MaruTama/ArduinoNameCard/res/img/3Dviewer.png

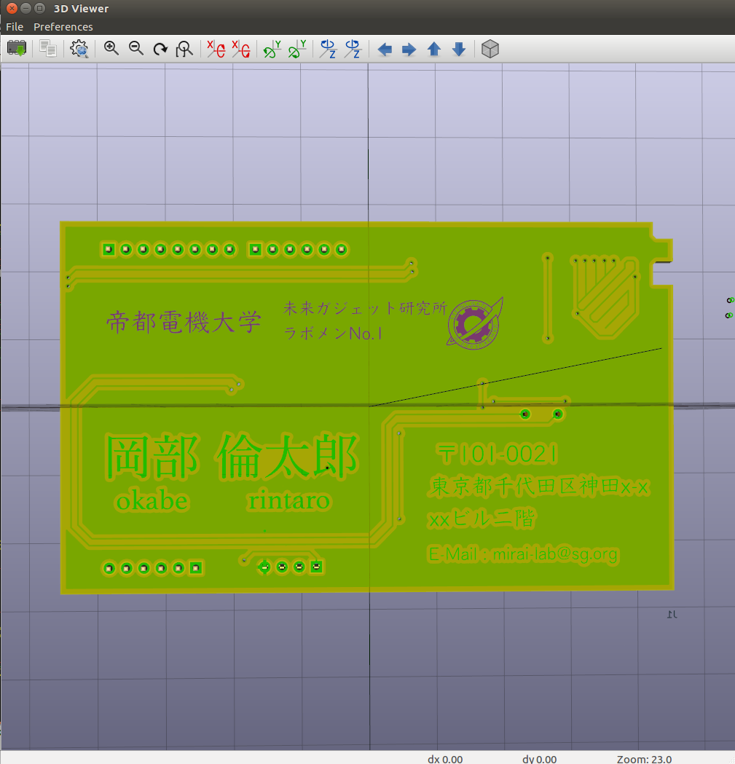
res/img/3Dviewer.png
