MaruTama/ArduinoNameCard/res/img/affiliation.png

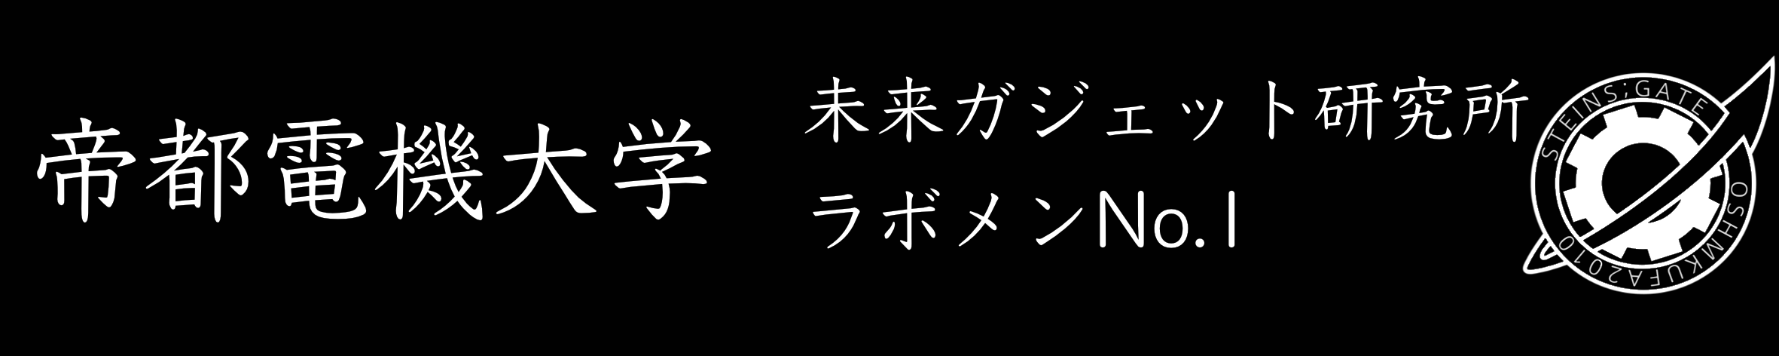
res/img/affiliation.png
