MaruTama/ArduinoNameCard/res/img/apply_footprint.png

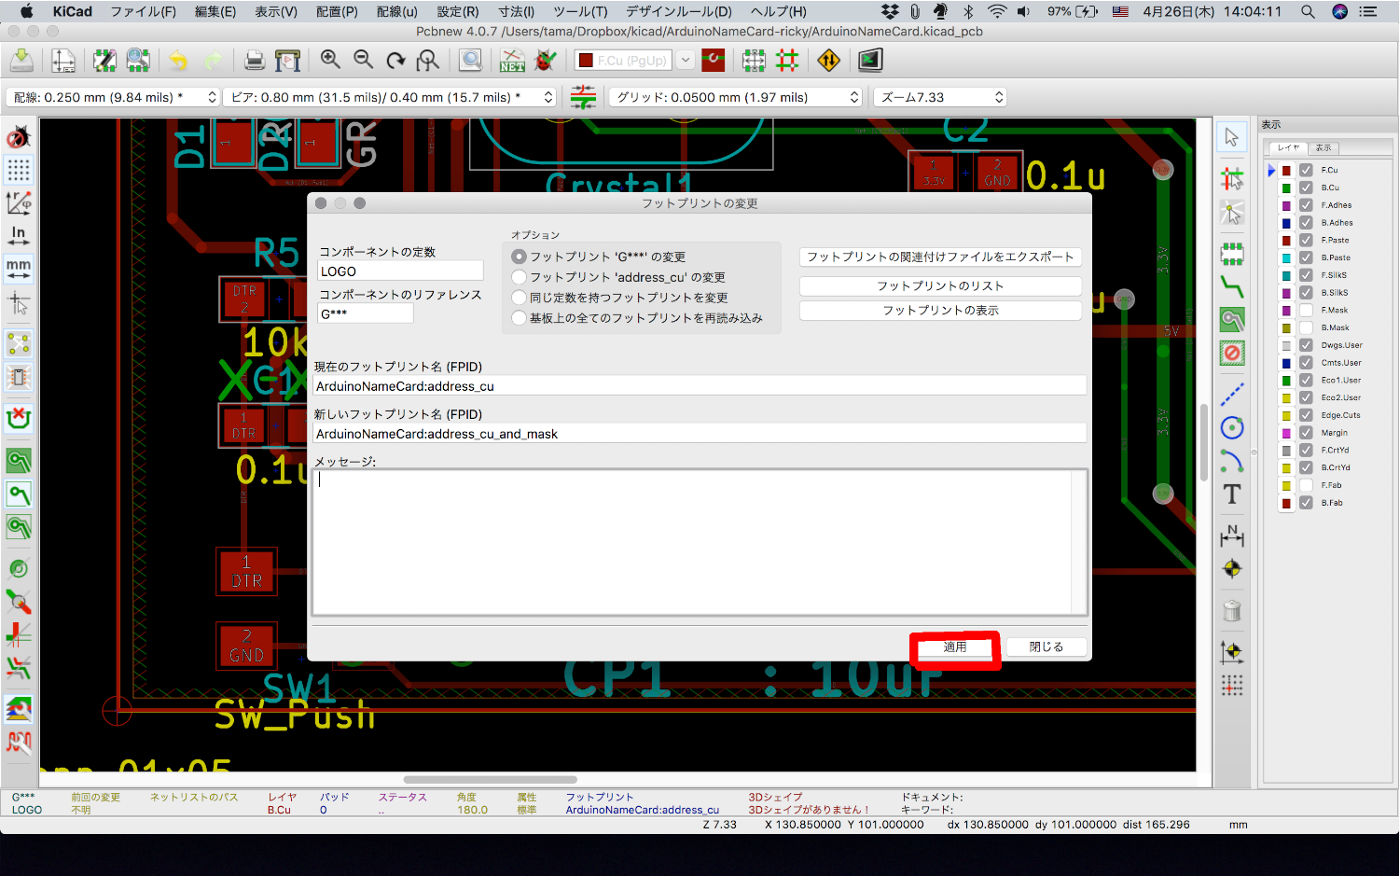
res/img/apply_footprint.png
