MaruTama/ArduinoNameCard/res/img/back_of_card.png

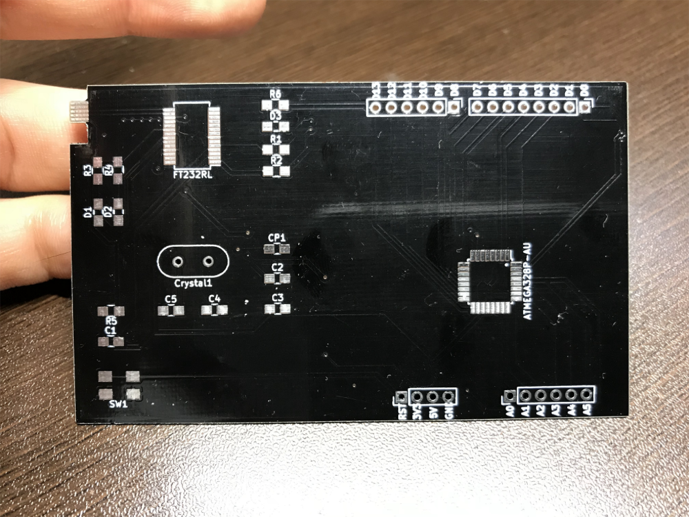
res/img/back_of_card.png
