MaruTama/ArduinoNameCard/res/img/bottom_black.png

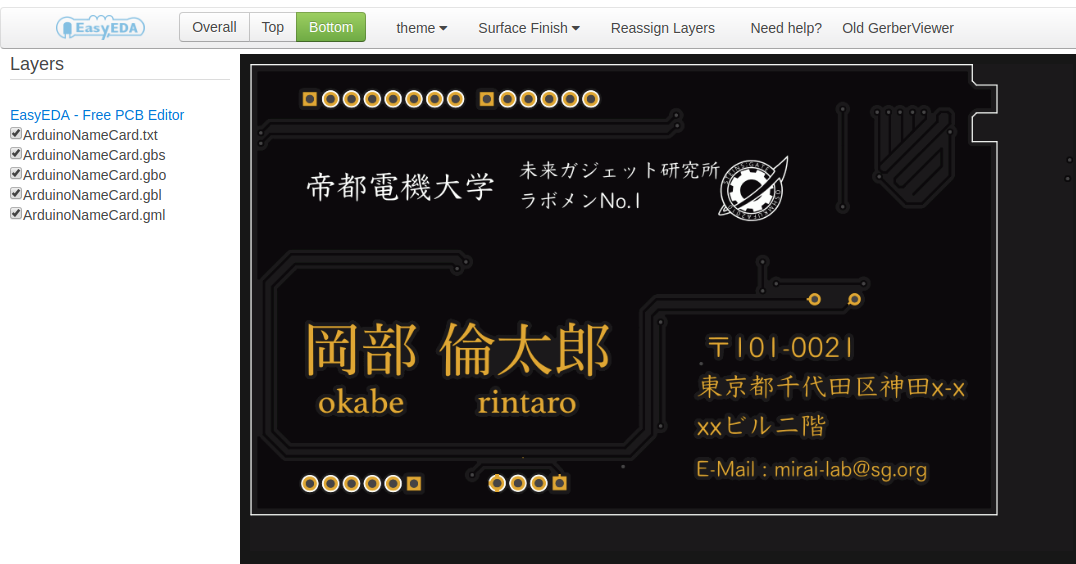
res/img/bottom_black.png
