MaruTama/ArduinoNameCard/res/img/change_footprint.png

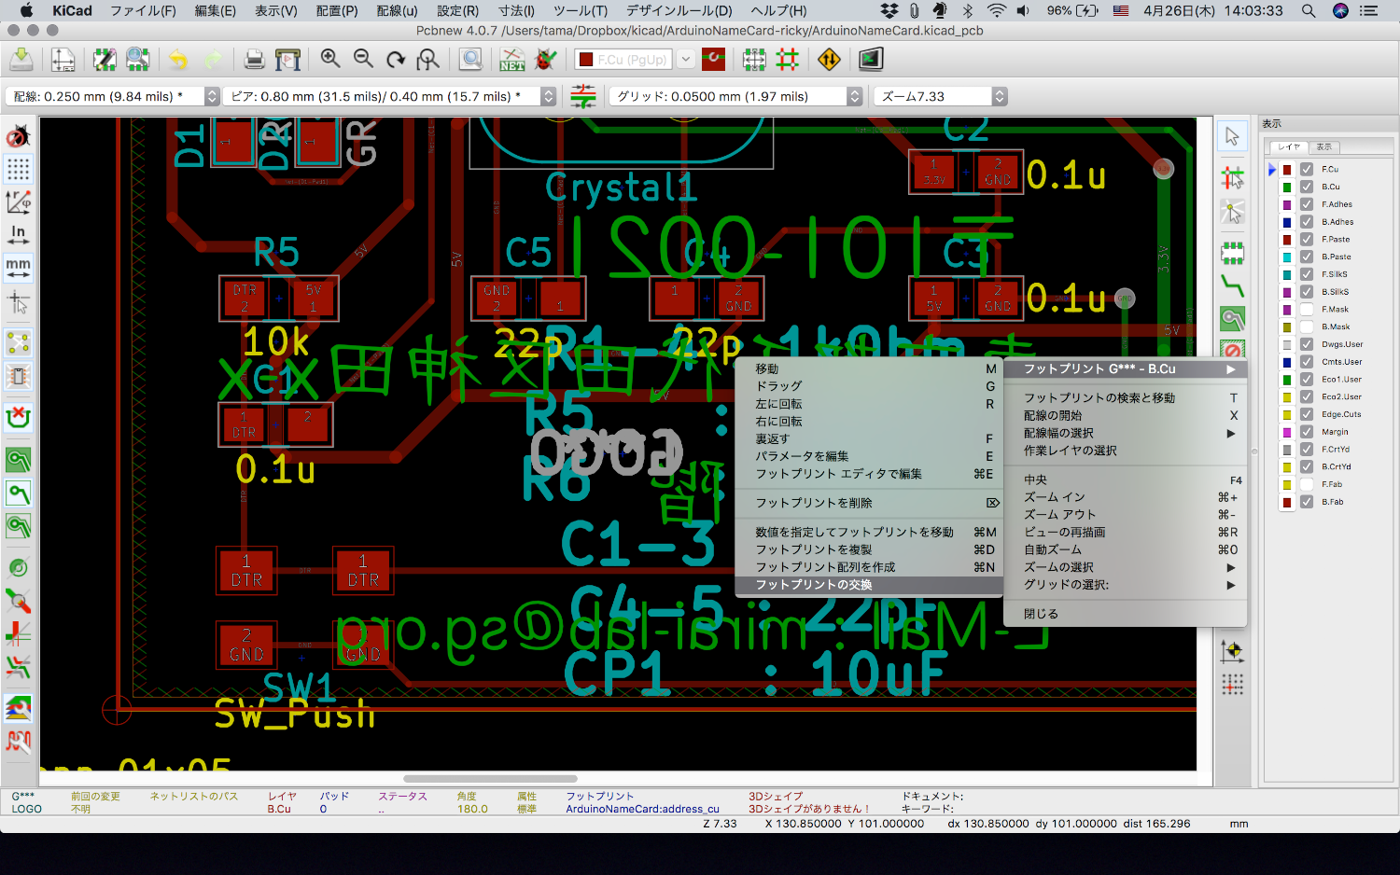
res/img/change_footprint.png
