MaruTama/ArduinoNameCard/res/img/create_img.png

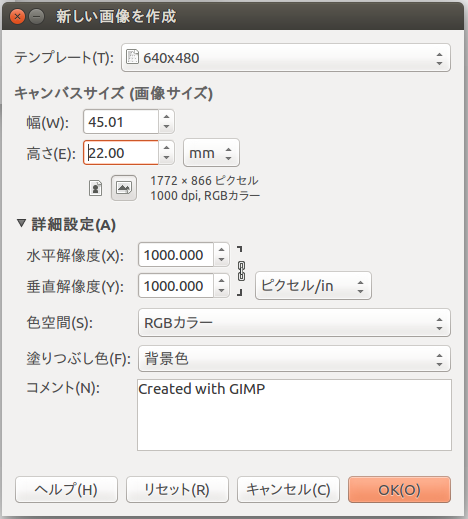
res/img/create_img.png
