MaruTama/ArduinoNameCard/res/img/flux.png

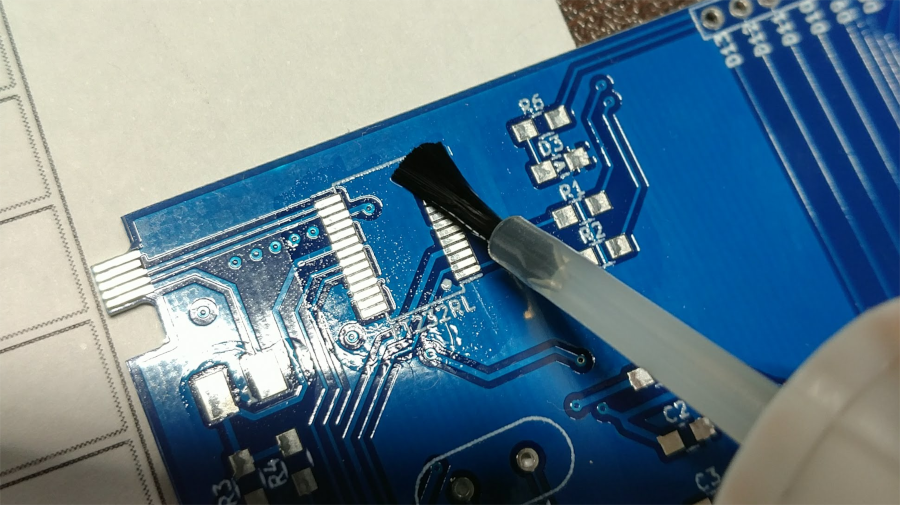
res/img/flux.png
