MaruTama/ArduinoNameCard/res/img/IMG_20180407_155647.jpg

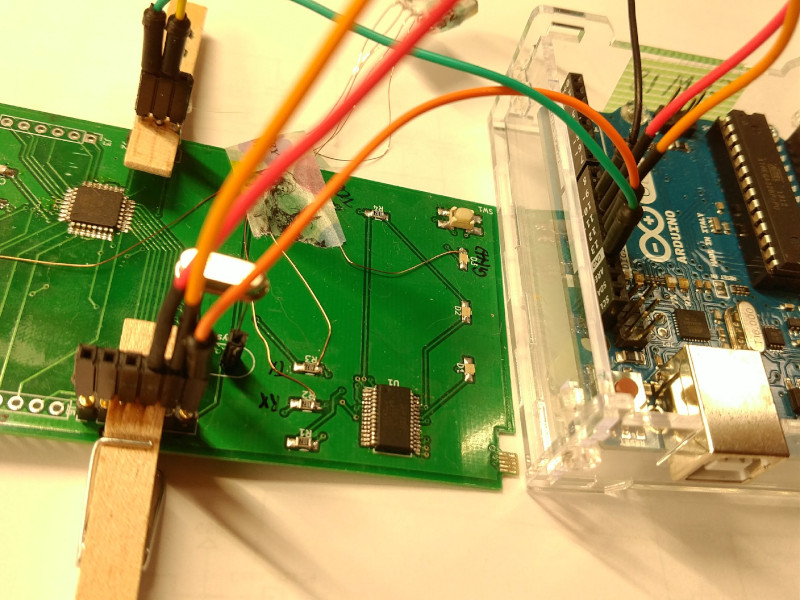
res/img/IMG_20180407_155647.jpg
