MaruTama/ArduinoNameCard/res/img/IMG_20180408_163213.jpg

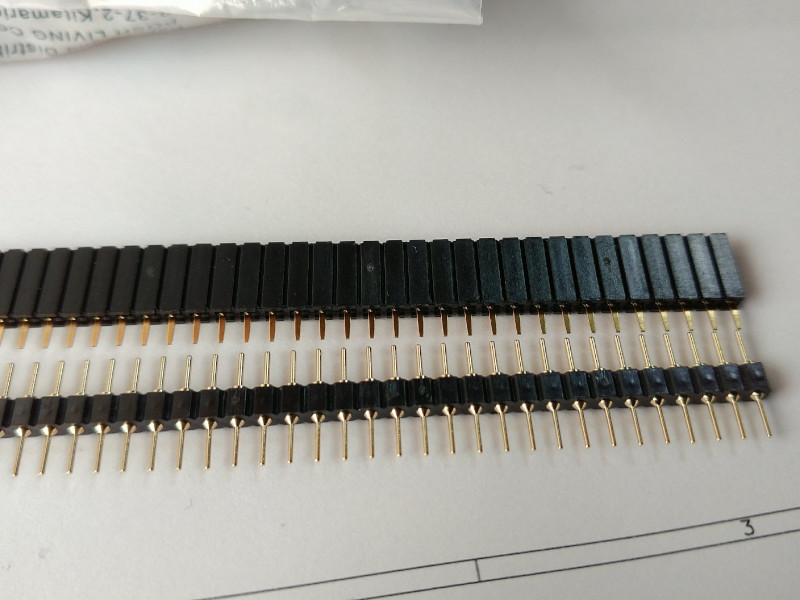
res/img/IMG_20180408_163213.jpg
