MaruTama/ArduinoNameCard/res/img/IMG_20180408_163228.jpg

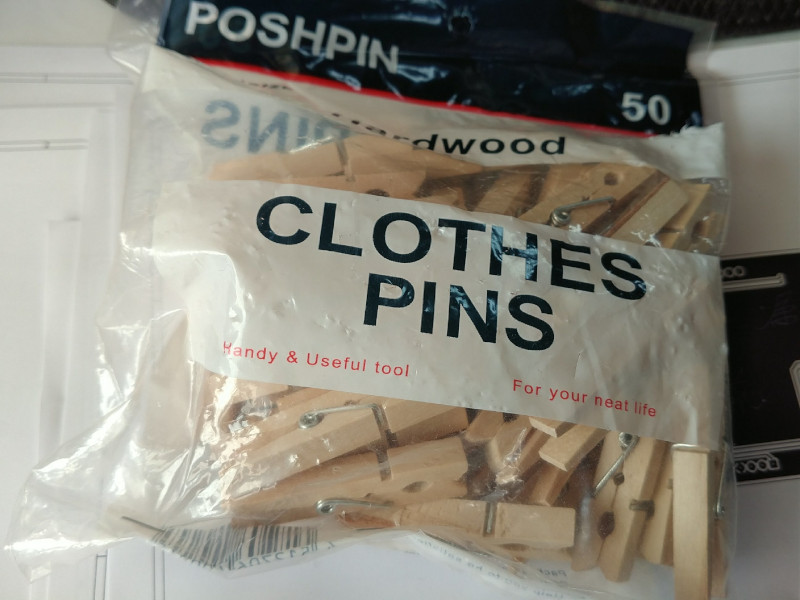
res/img/IMG_20180408_163228.jpg
