MaruTama/ArduinoNameCard/res/img/IMG_20180408_163235.jpg

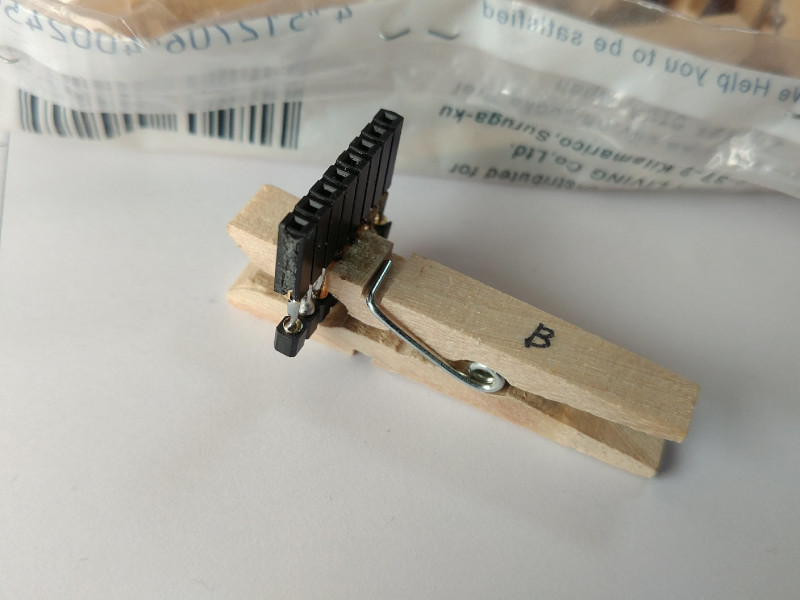
res/img/IMG_20180408_163235.jpg
