MaruTama/ArduinoNameCard/res/img/import1.png

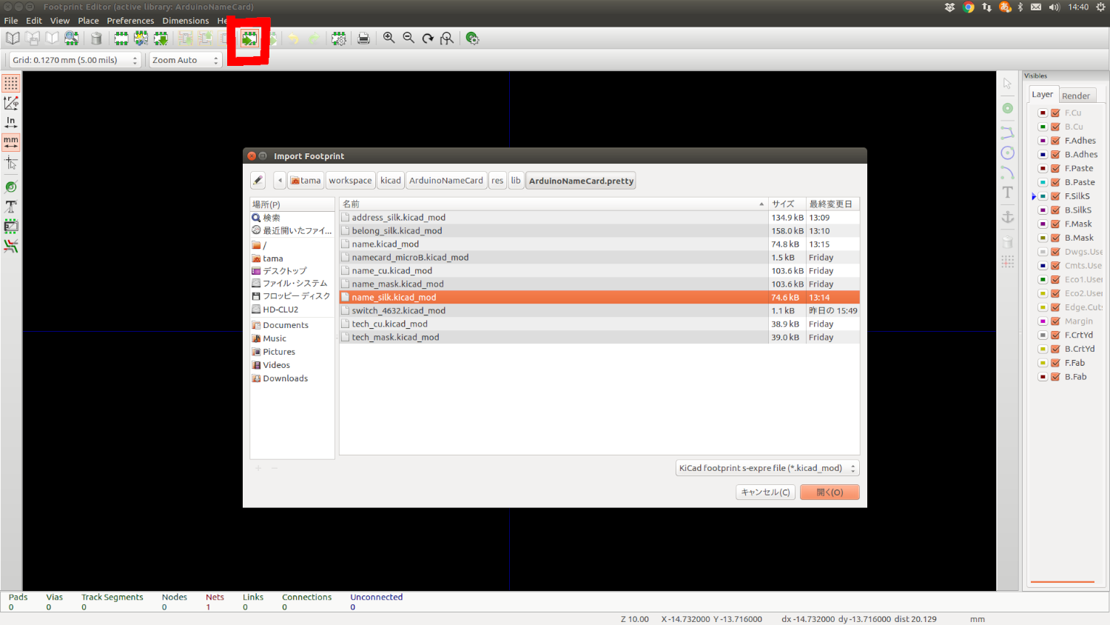
res/img/import1.png
