MaruTama/ArduinoNameCard/res/img/import2.png

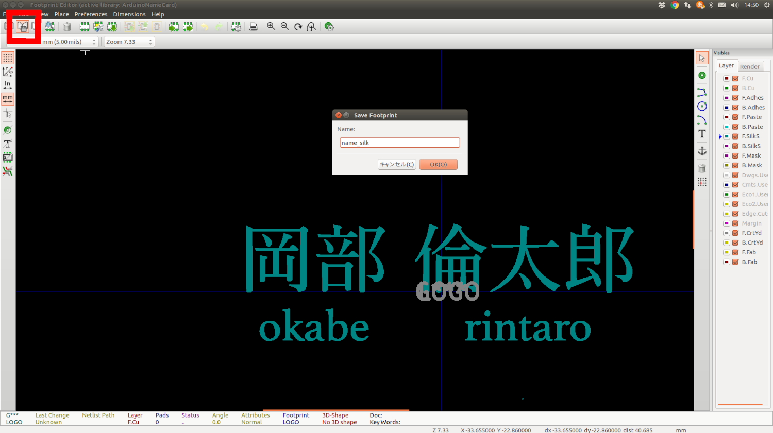
res/img/import2.png
