MaruTama/ArduinoNameCard/res/img/input_fig.png

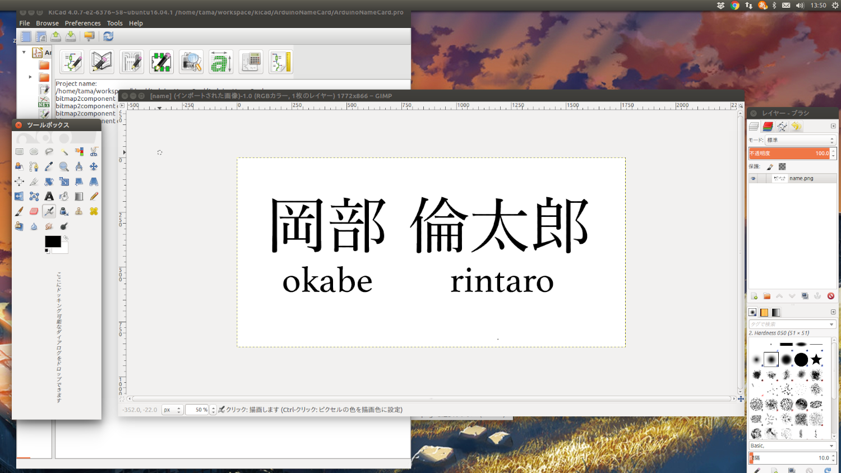
res/img/input_fig.png
