MaruTama/ArduinoNameCard/res/img/invert_img.png

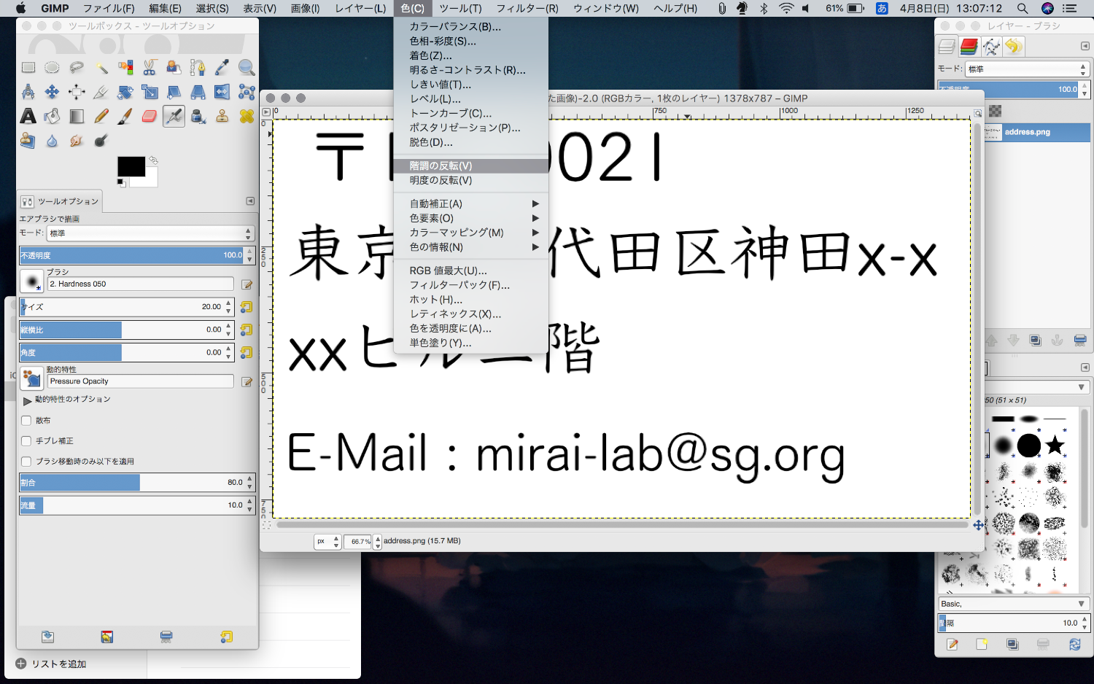
res/img/invert_img.png
