MaruTama/ArduinoNameCard/res/img/list_of_footprint.png

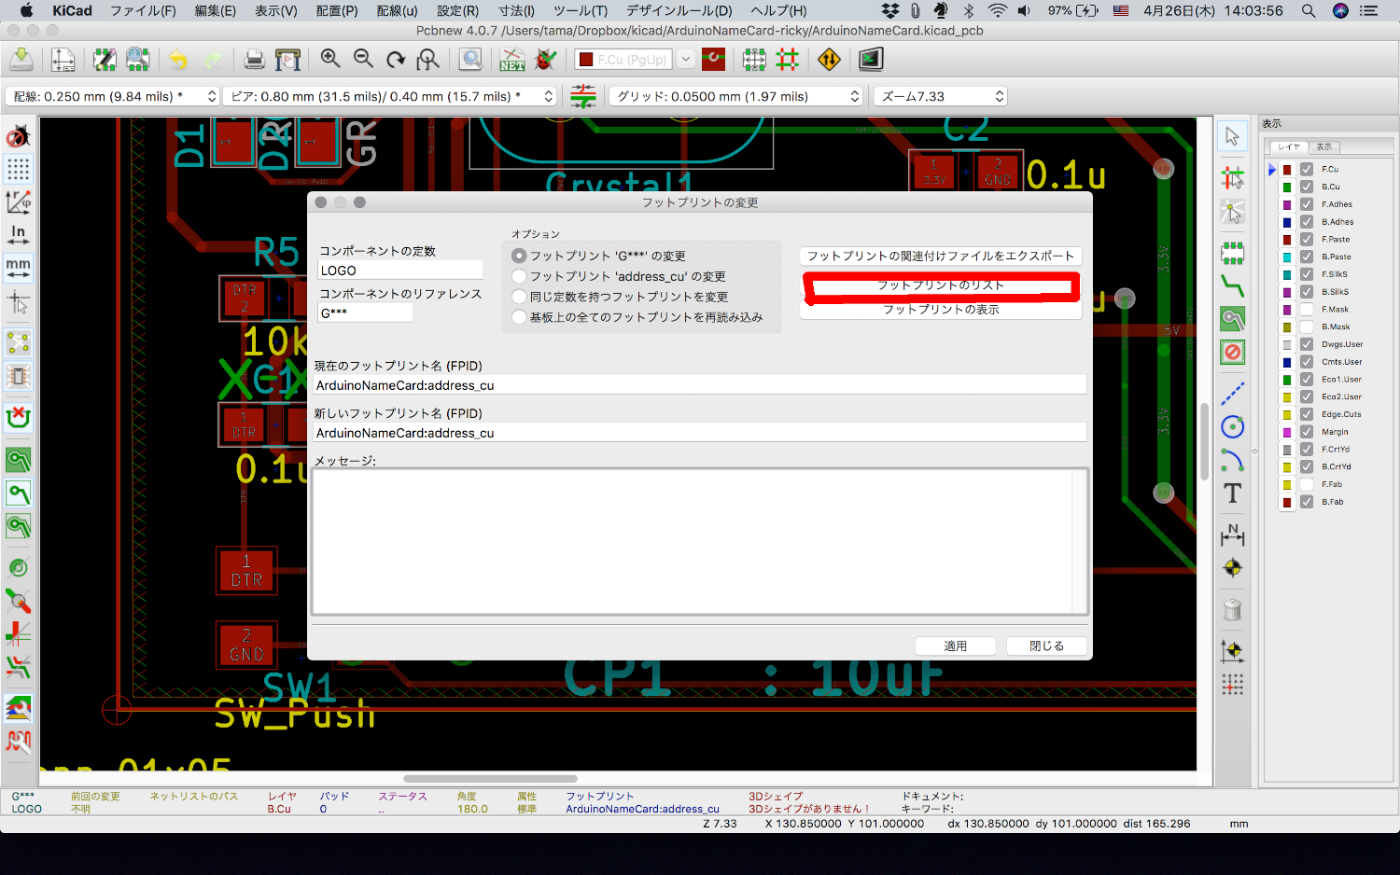
res/img/list_of_footprint.png
