MaruTama/ArduinoNameCard/res/img/name.png

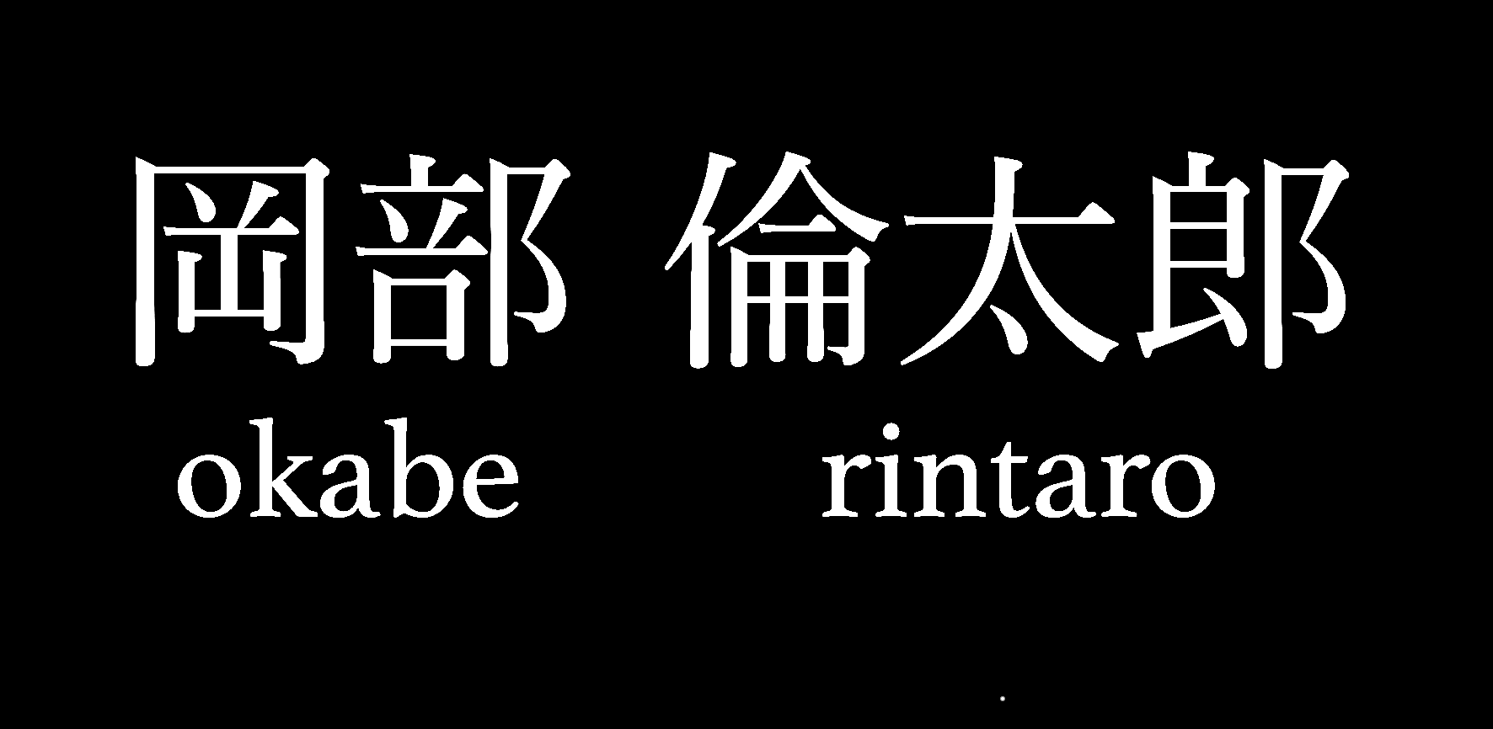
res/img/name.png
