MaruTama/ArduinoNameCard/res/img/output_drill.png

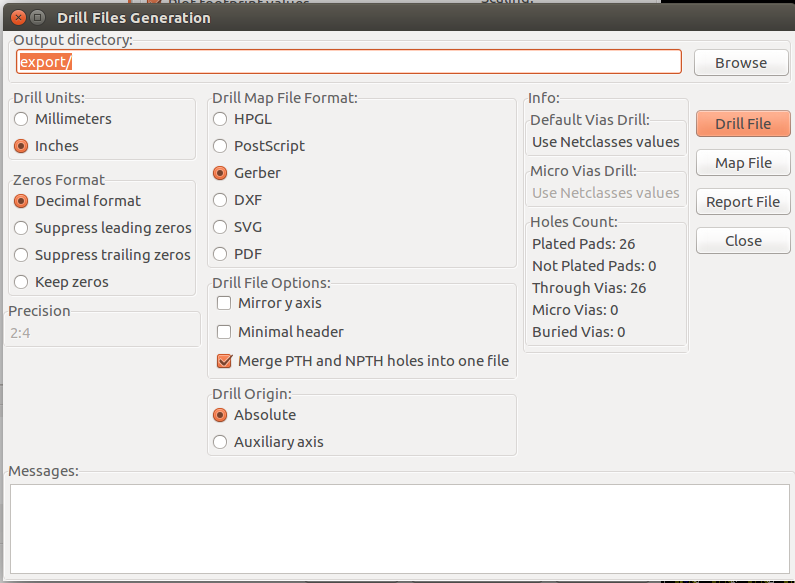
res/img/output_drill.png
