MaruTama/ArduinoNameCard/res/img/output_gerver.png

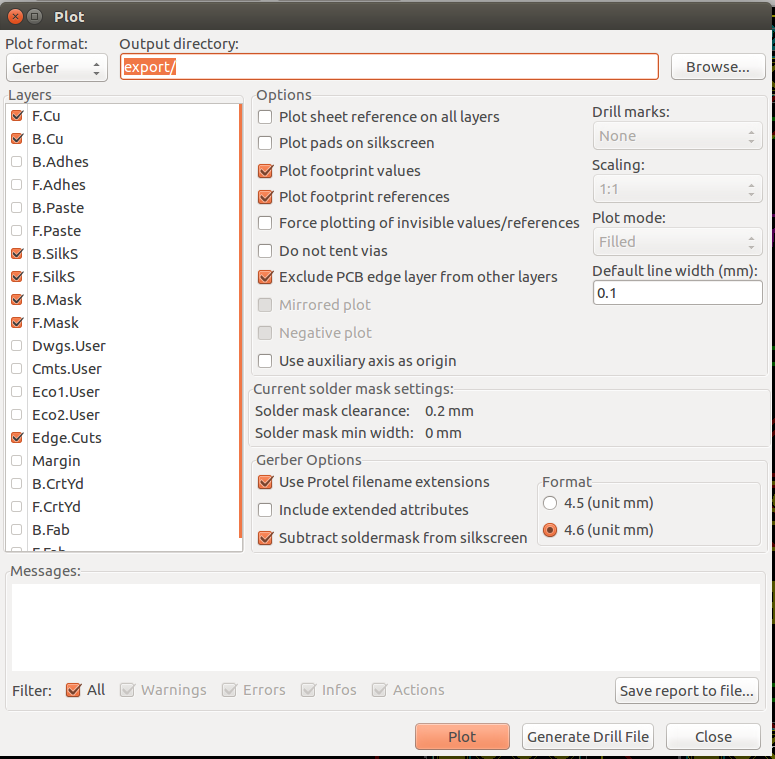
res/img/output_gerver.png
