MaruTama/ArduinoNameCard/res/img/put_on_ic.png

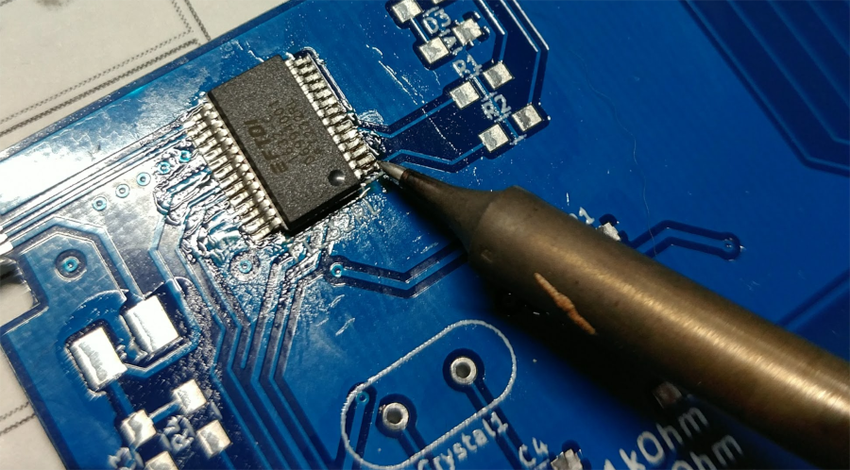
res/img/put_on_ic.png
