MaruTama/ArduinoNameCard/res/img/rename_mask2cu.png

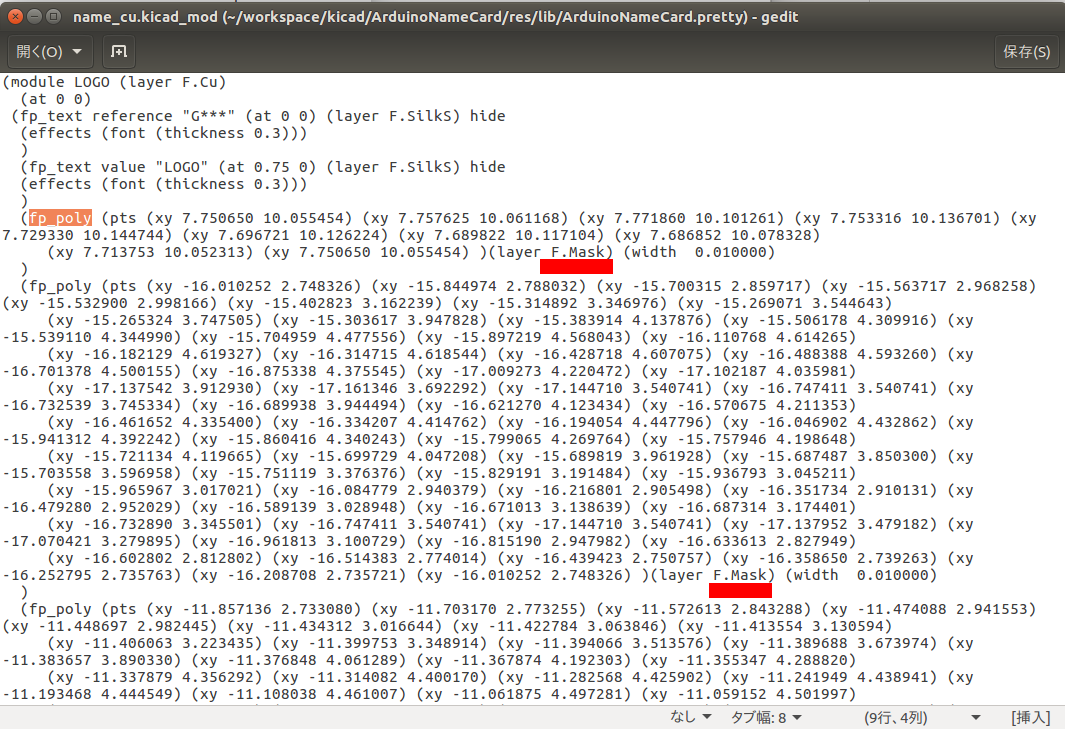
res/img/rename_mask2cu.png
