MaruTama/ArduinoNameCard/res/img/renamed.png

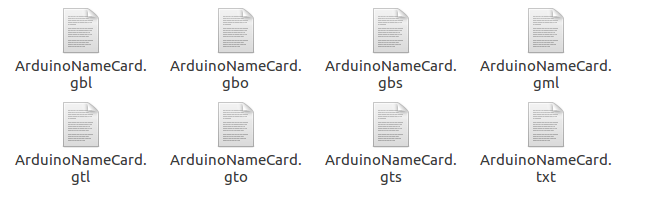
res/img/renamed.png
