MaruTama/ArduinoNameCard/res/img/win_choco.png

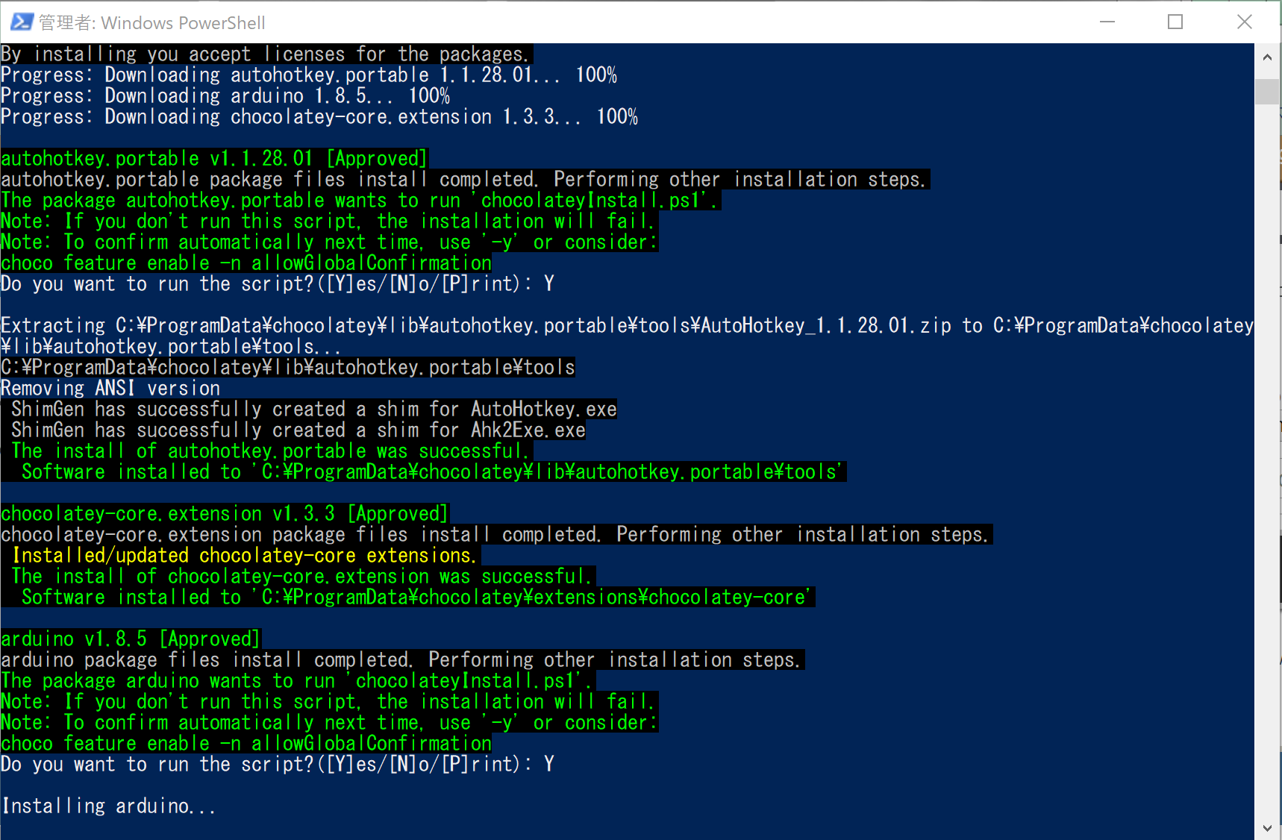
res/img/win_choco.png
