MaruTama/ArduinoNameCard/res/img/win_driver.png

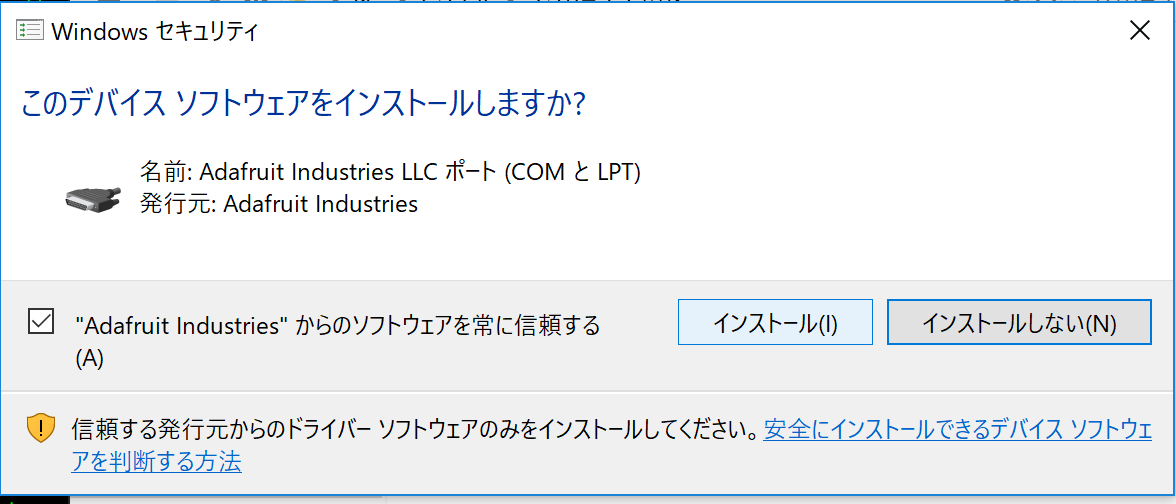
res/img/win_driver.png
