MaruTama/ArduinoNameCard/res/img/make_mask.png

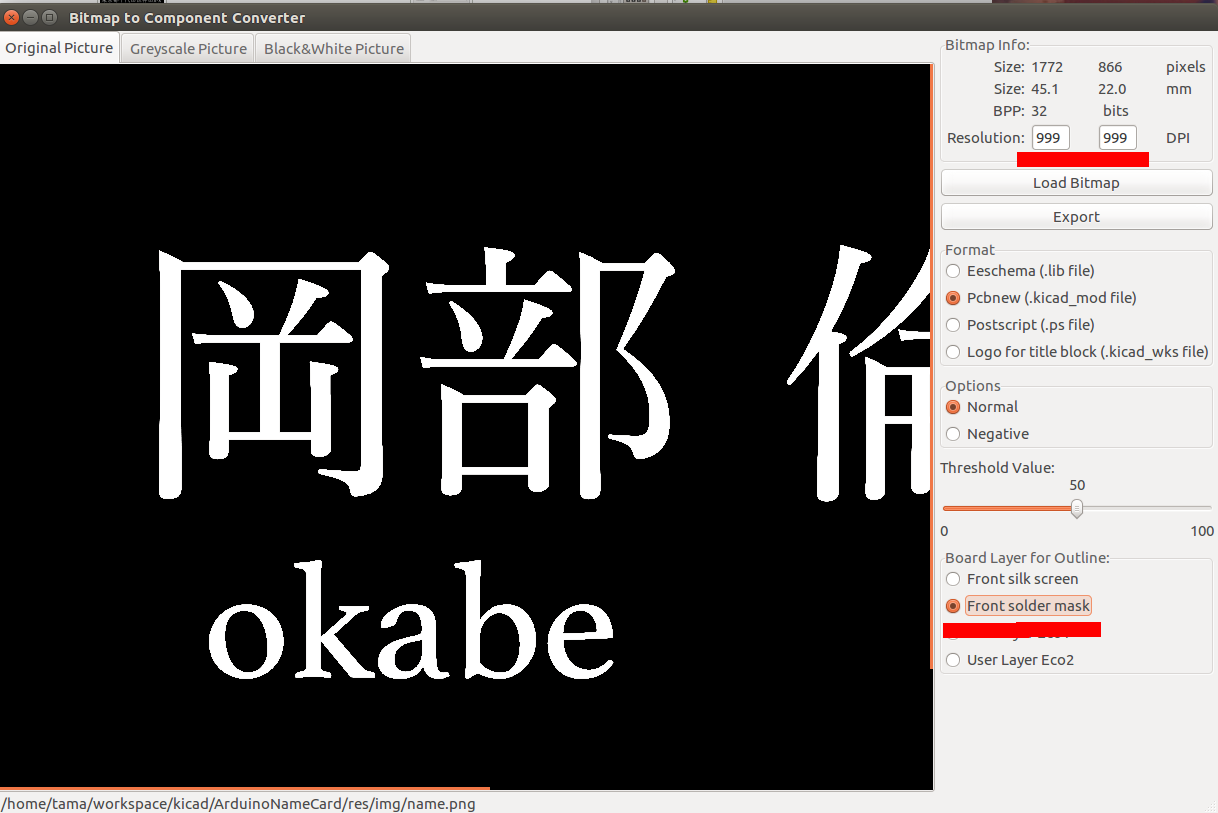
res/img/make_mask.png
