MaruTama/ArduinoNameCard/res/img/solder.png

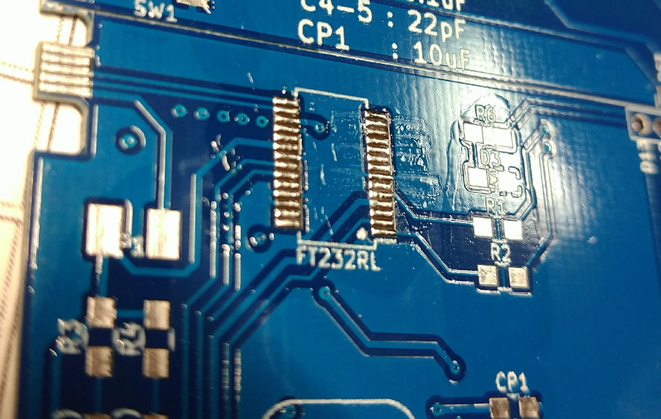
res/img/solder.png
